challengethecyber/ctf-2023-badge/hardware/USB-C-Connectors-master/images/TypeC-power.png

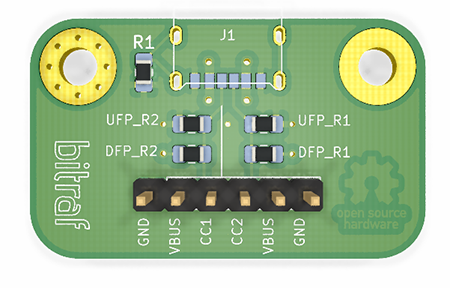
hardware/USB-C-Connectors-master/images/TypeC-power.png
