challengethecyber/ctf-2023-badge/hardware/USB-C-Connectors-master/images/2.0_vs_3.0.jpg

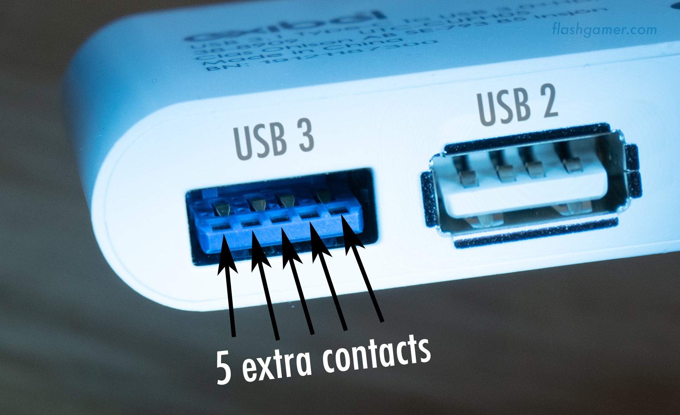
hardware/USB-C-Connectors-master/images/2.0_vs_3.0.jpg
