challengethecyber/ctf-2023-badge/hardware/psd/v2-duck-10cm-bw.png

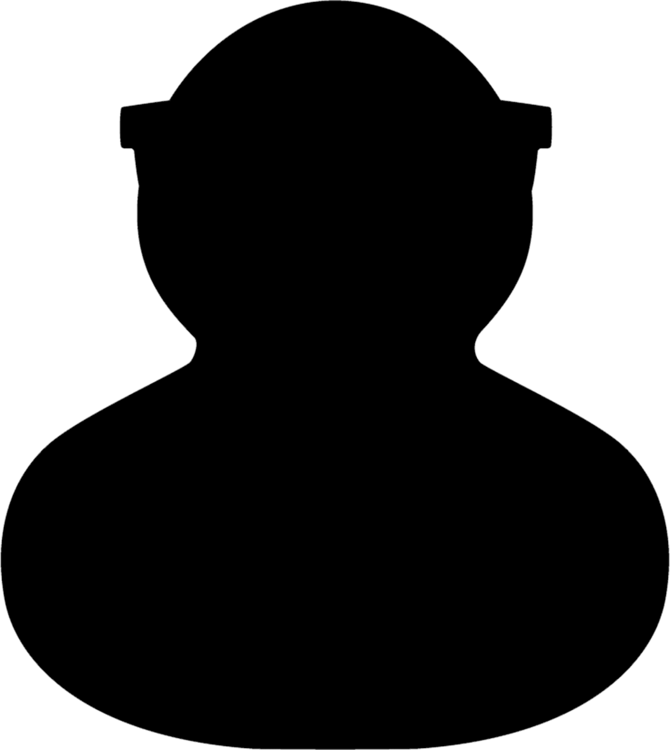
hardware/psd/v2-duck-10cm-bw.png
