challengethecyber/ctf-2023-badge/hardware/psd/v2-duck-10cm-lines-noarms-nomouth.png

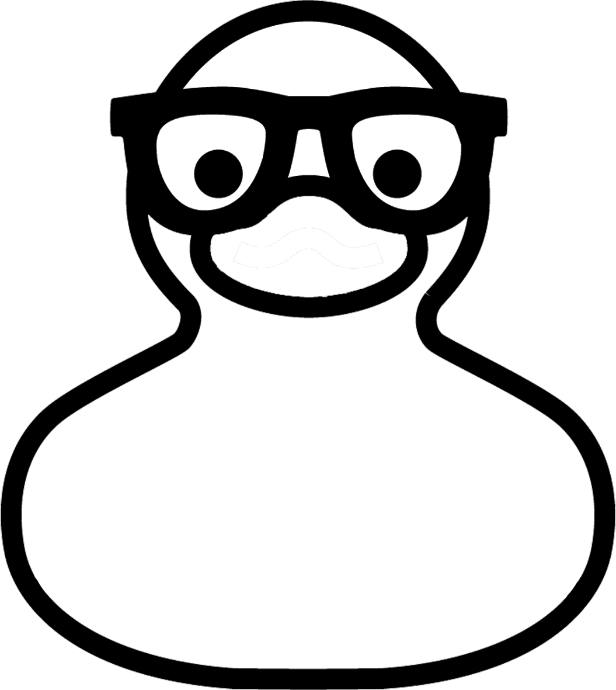
hardware/psd/v2-duck-10cm-lines-noarms-nomouth.png
