challengethecyber/ctf-2023-badge/hardware/USB-C-Connectors-master/images/TypeC-USB2.0.png

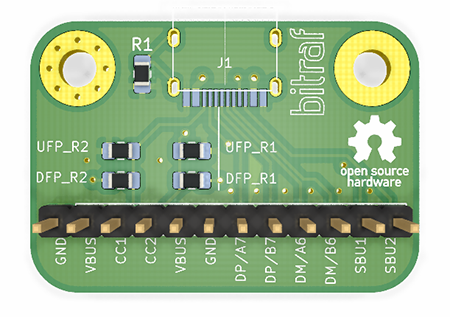
hardware/USB-C-Connectors-master/images/TypeC-USB2.0.png
