challengethecyber/ctf-2023-badge/hardware/USB-C-Connectors-master/images/TypeC-USB3.1.png

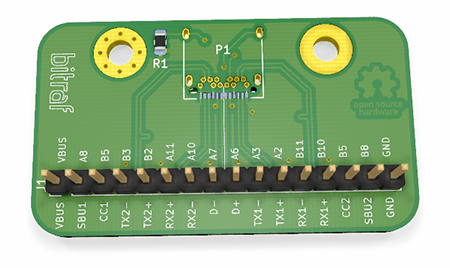
hardware/USB-C-Connectors-master/images/TypeC-USB3.1.png
