challengethecyber/ctf-2023-badge/hardware/USB-C-Connectors-master/images/USB-C_pinout.png

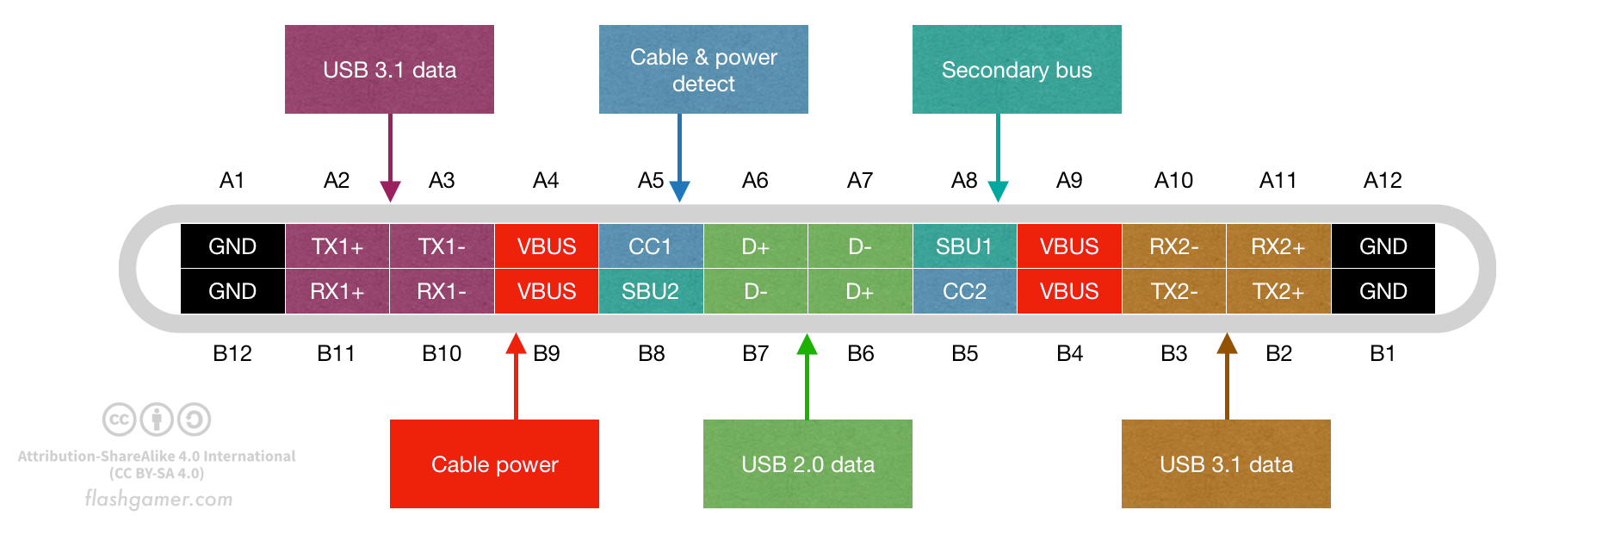
hardware/USB-C-Connectors-master/images/USB-C_pinout.png
